oddsocks1024/StickleBack/images/2.jpg

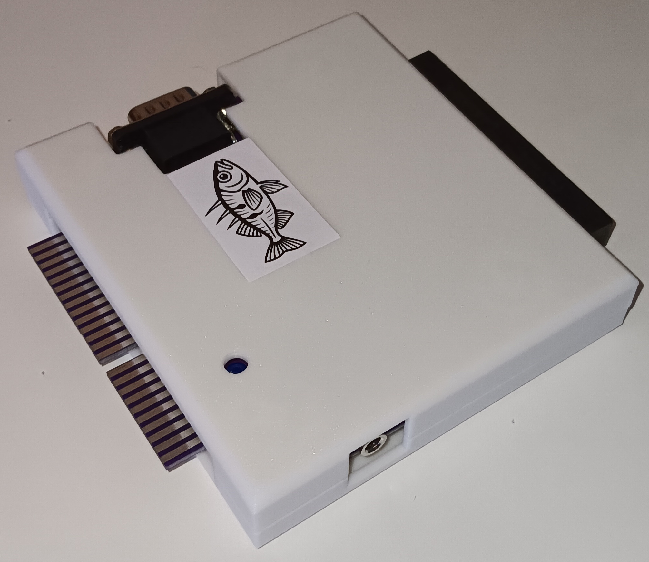
images/2.jpg
