oddsocks1024/StickleBack/images/3.jpg

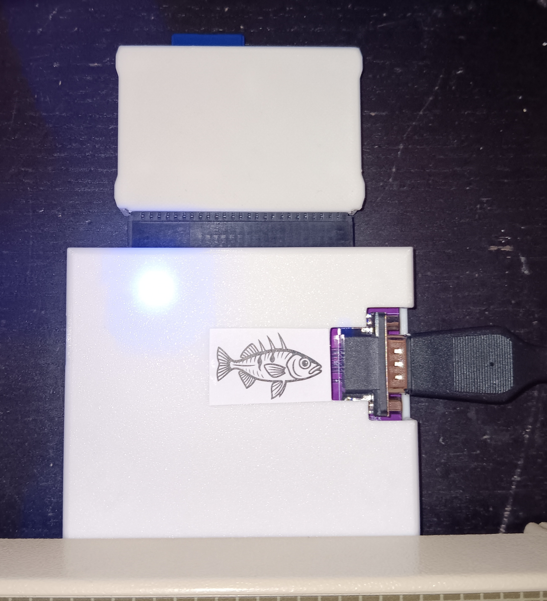
images/3.jpg
